sillyhatday/IN-12-NIXIE-CLOCK/PHOTOS & RENDERS/Nixie clock assembled rear.png

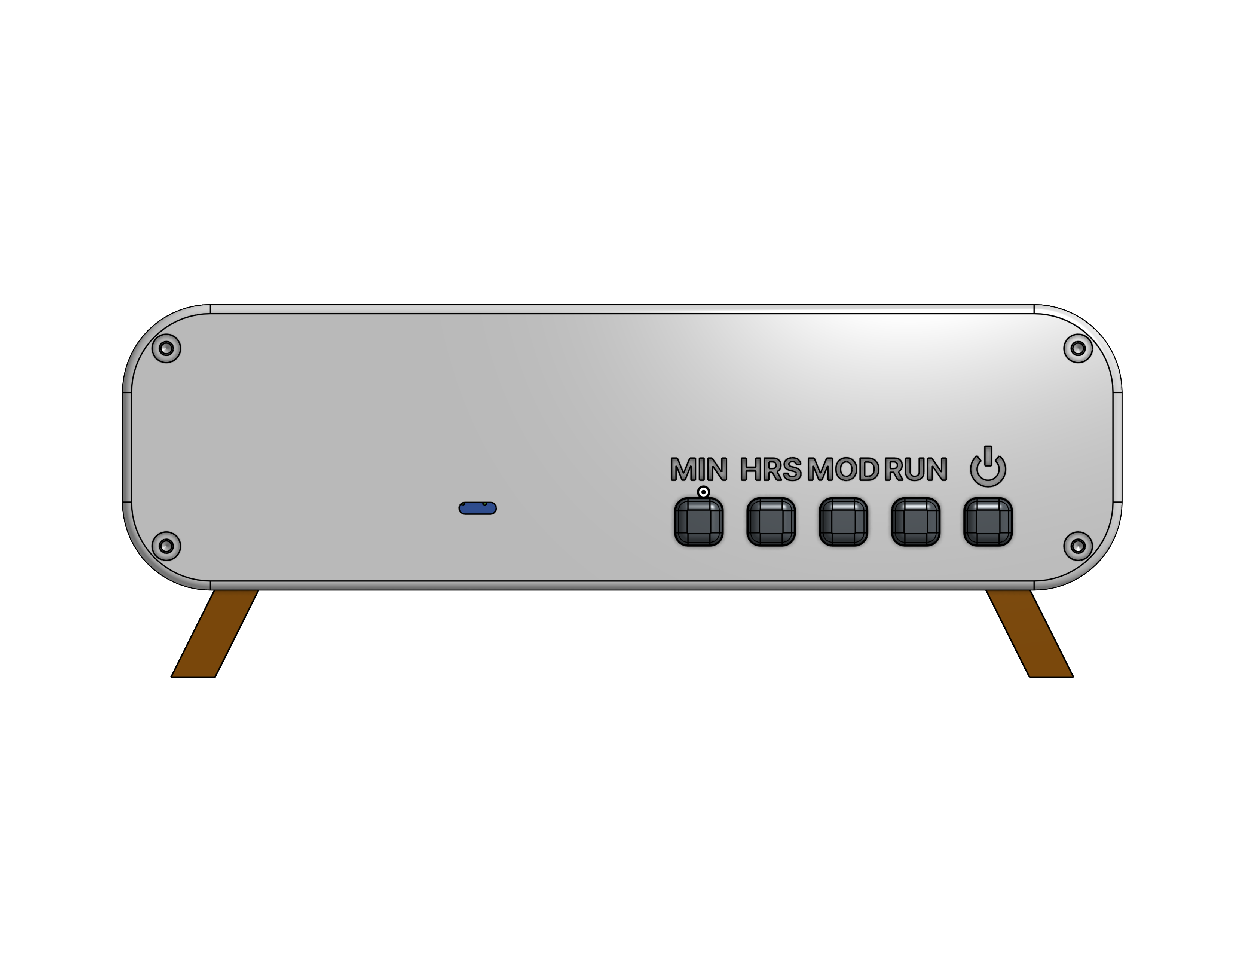
PHOTOS & RENDERS/Nixie clock assembled rear.png
