sillyhatday/IN-12-NIXIE-CLOCK/PHOTOS & RENDERS/Nixie clock assembled.png

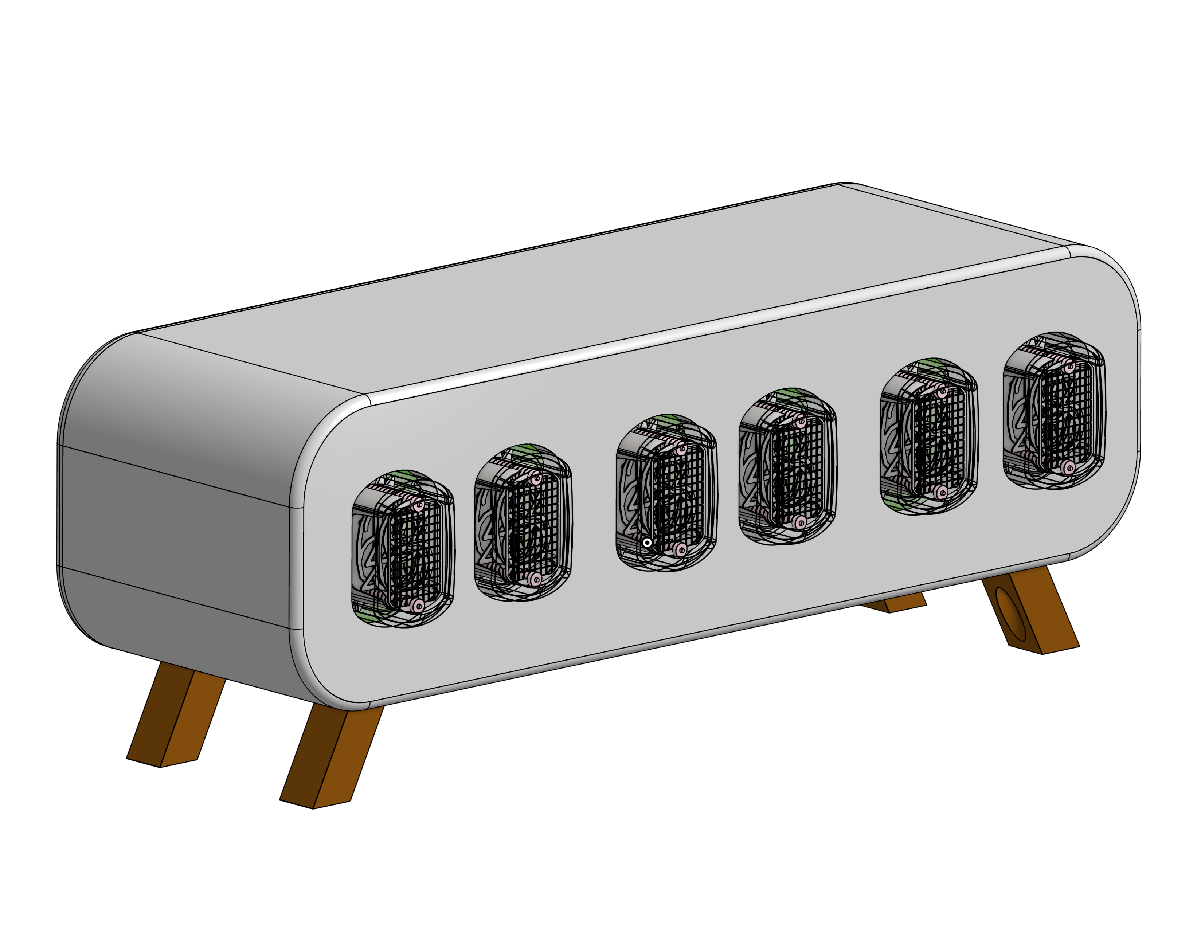
PHOTOS & RENDERS/Nixie clock assembled.png
